tbkfi/isd-carrier/output/v0.1/integration-testing/bom1.png

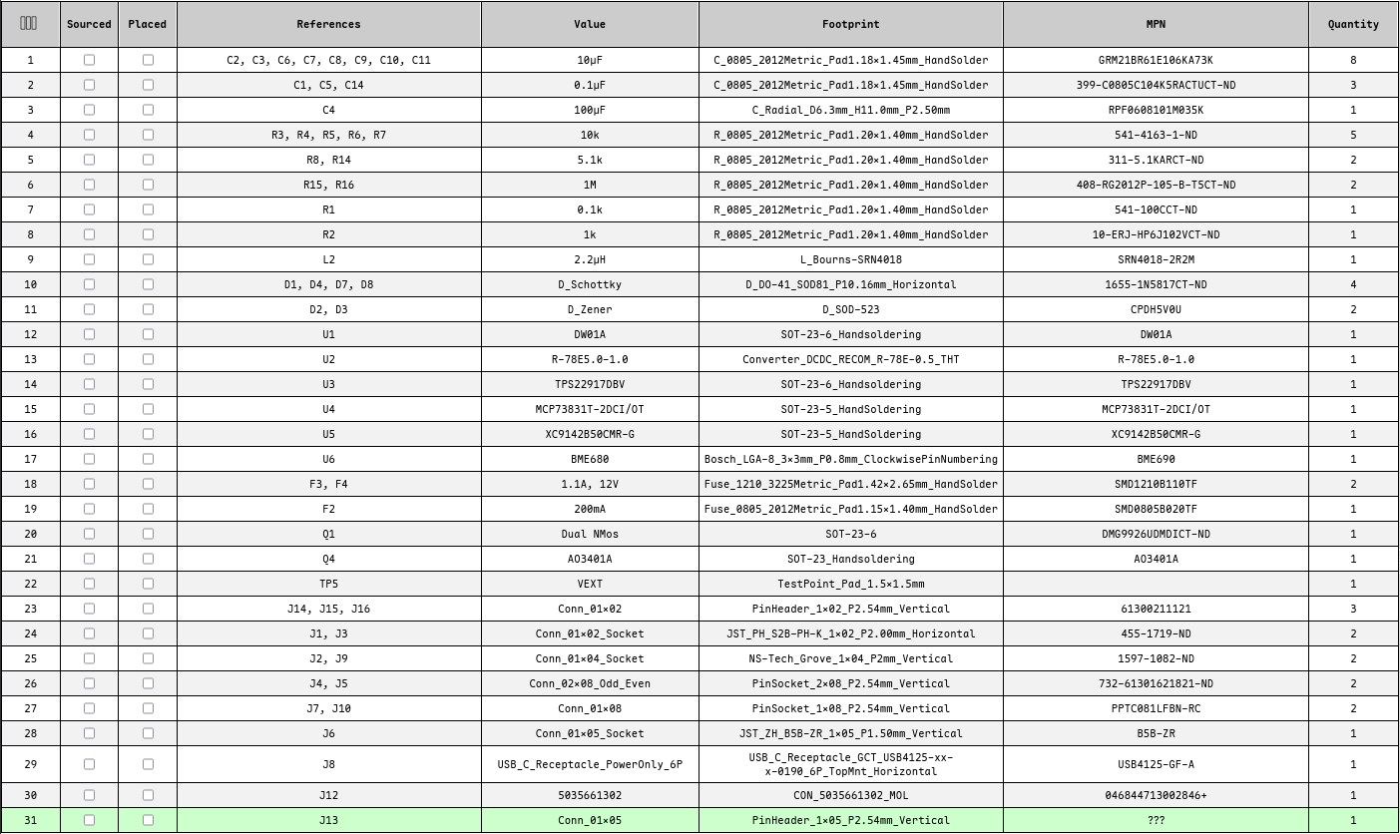
output/v0.1/integration-testing/bom1.png
