tbkfi/isd-carrier/output/v0.1/integration-testing/bom2.png

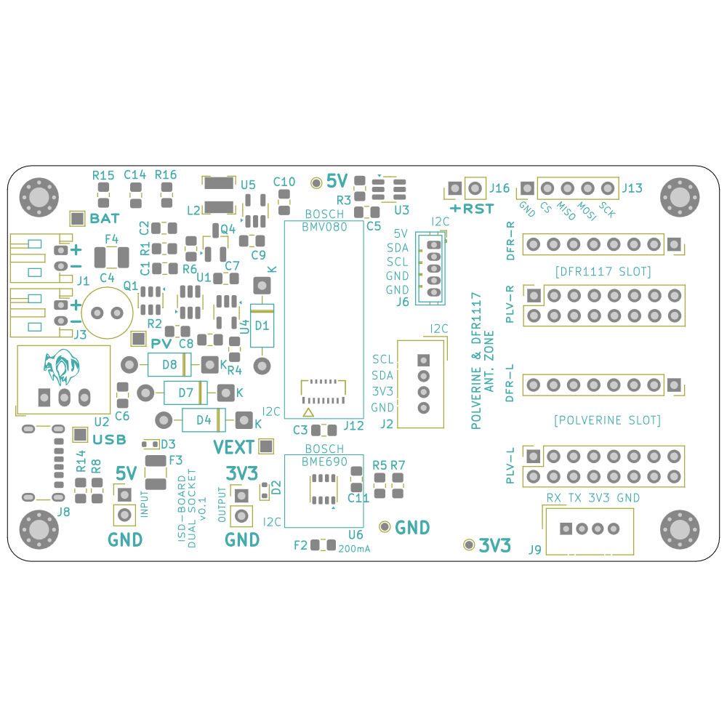
output/v0.1/integration-testing/bom2.png
